djgreeb/Technics_SL-DZ1200_new_life/CNC/Spindel/shpinder.jpg

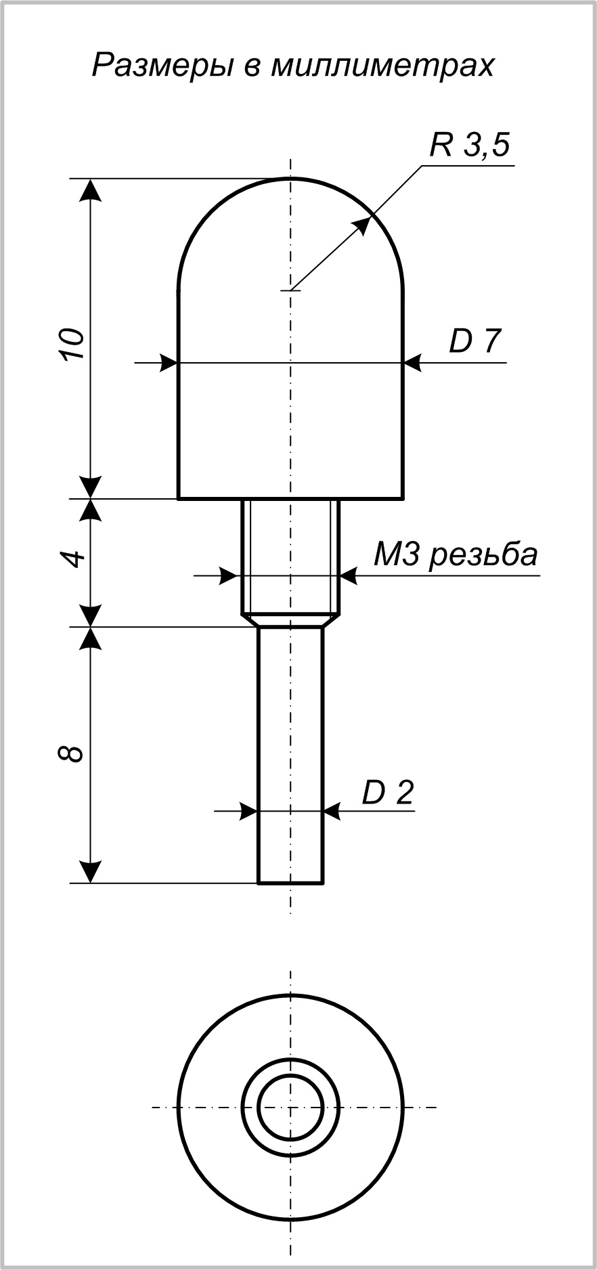
CNC/Spindel/shpinder.jpg
