djgreeb/Technics_SL-DZ1200_new_life/KiCad pcb project/SLDZ_Lay2.jpg

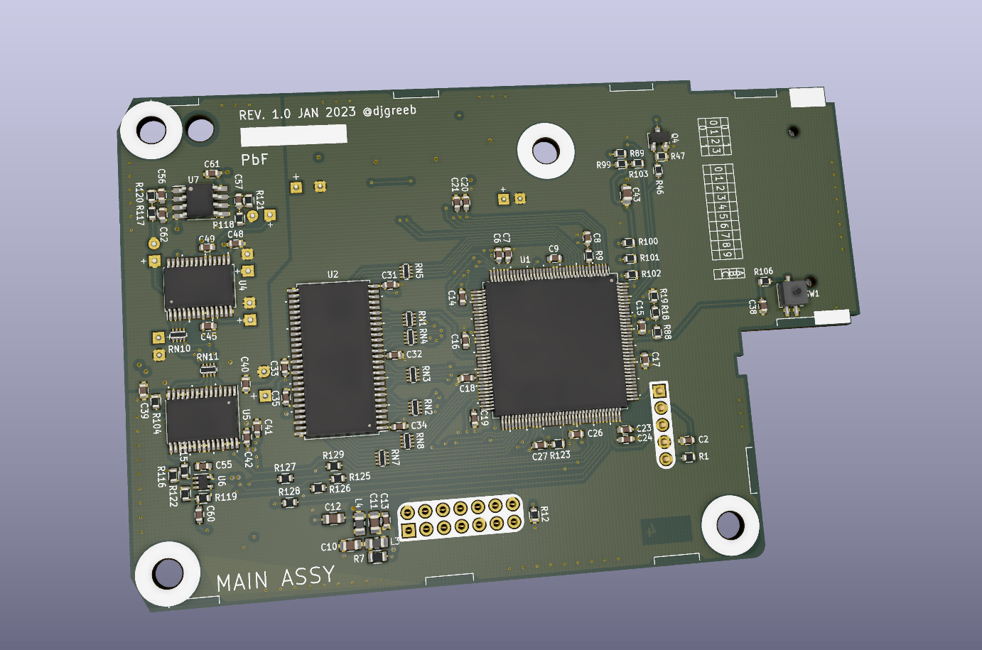
KiCad pcb project/SLDZ_Lay2.jpg
