djgreeb/Technics_SL-DZ1200_new_life/notes/Direct Drive signal control.JPG

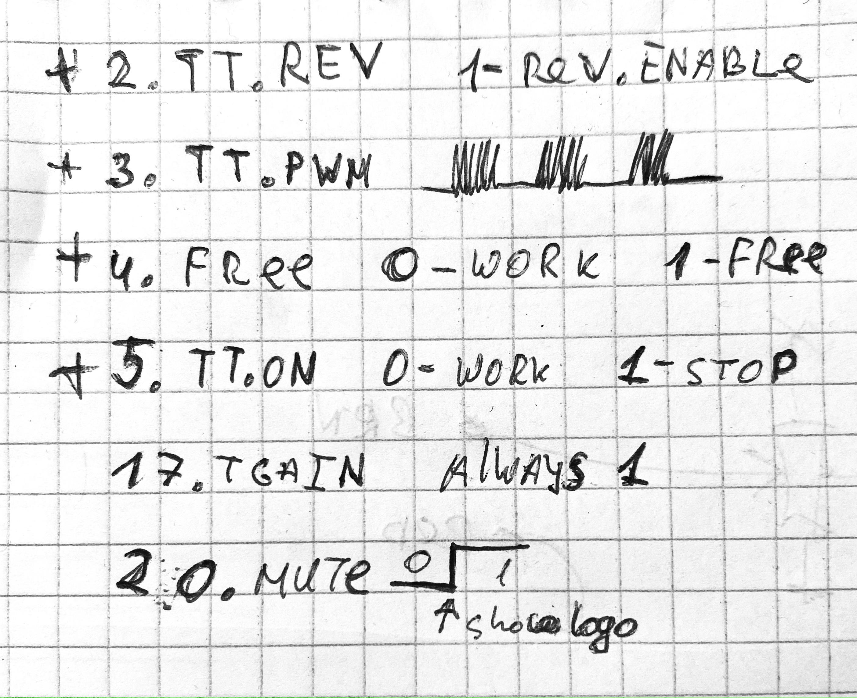
notes/Direct Drive signal control.JPG
