djgreeb/Technics_SL-DZ1200_new_life/Original DAC init data/DAC init.JPG

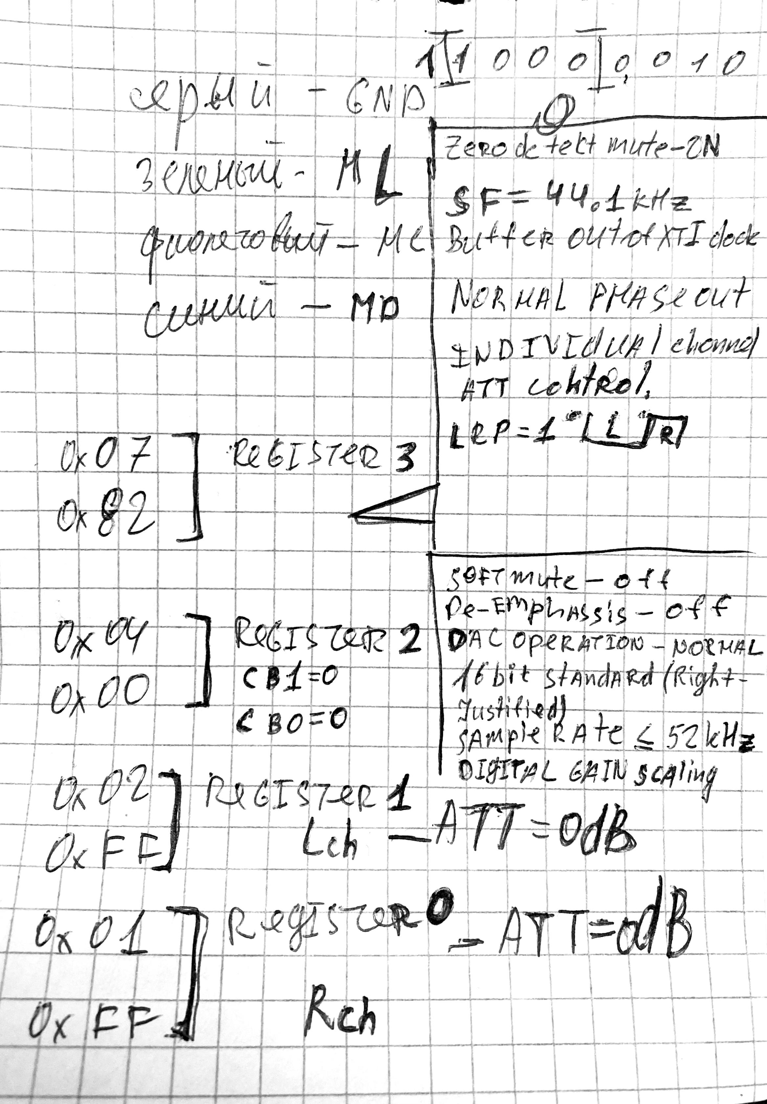
Original DAC init data/DAC init.JPG
