djgreeb/Technics_SL-DZ1200_new_life/Photo/IMG_2577.jpg

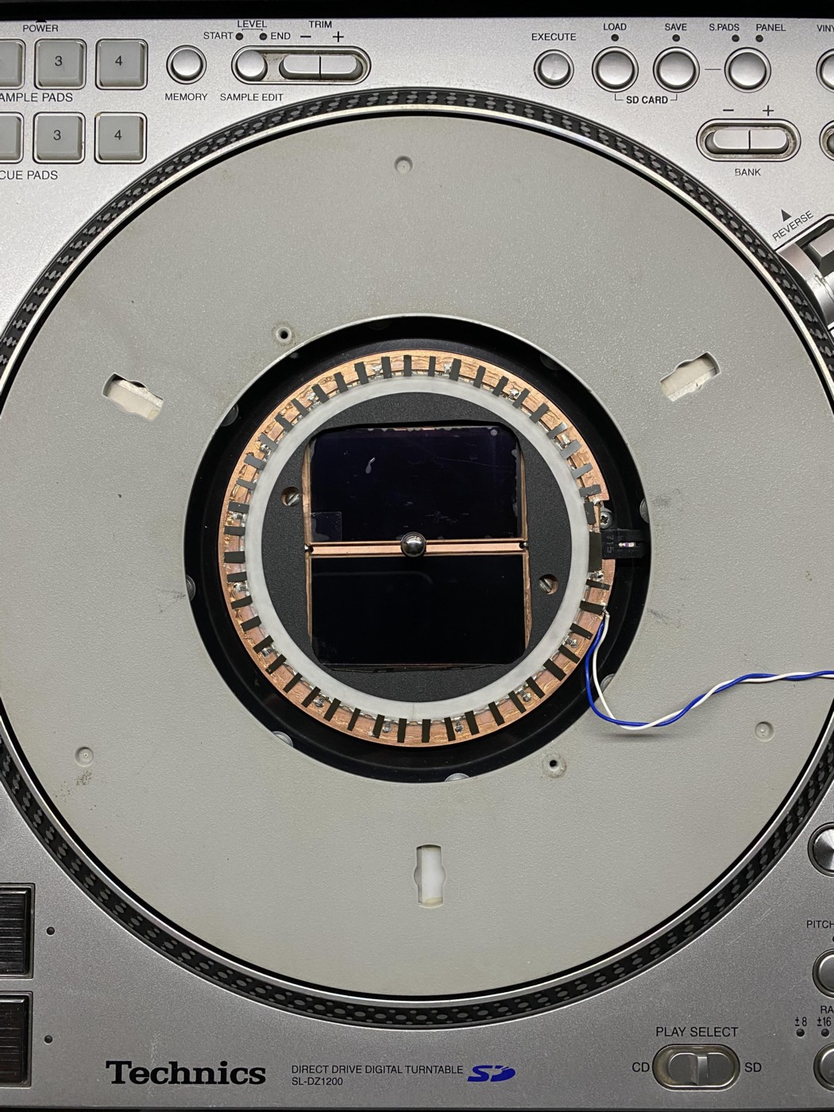
Photo/IMG_2577.jpg
