djgreeb/Technics_SL-DZ1200_new_life/Photo/IMG_2646.jpg

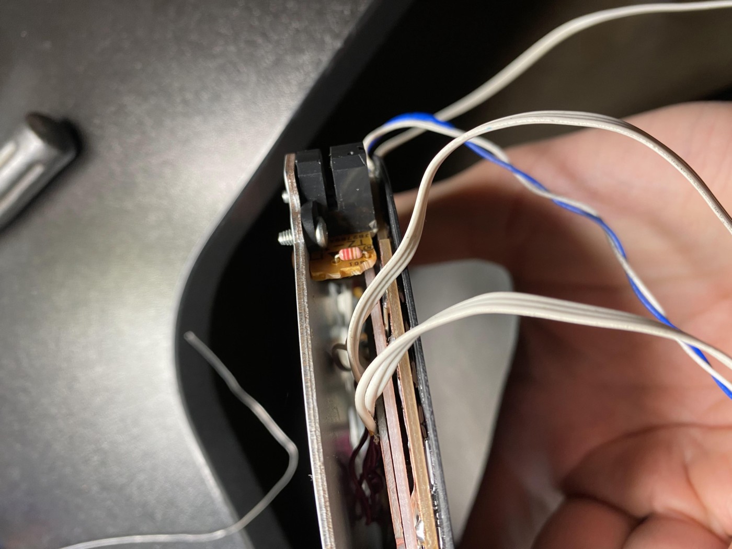
Photo/IMG_2646.jpg
