djgreeb/Technics_SL-DZ1200_new_life/Photo/IMG_2647.jpg

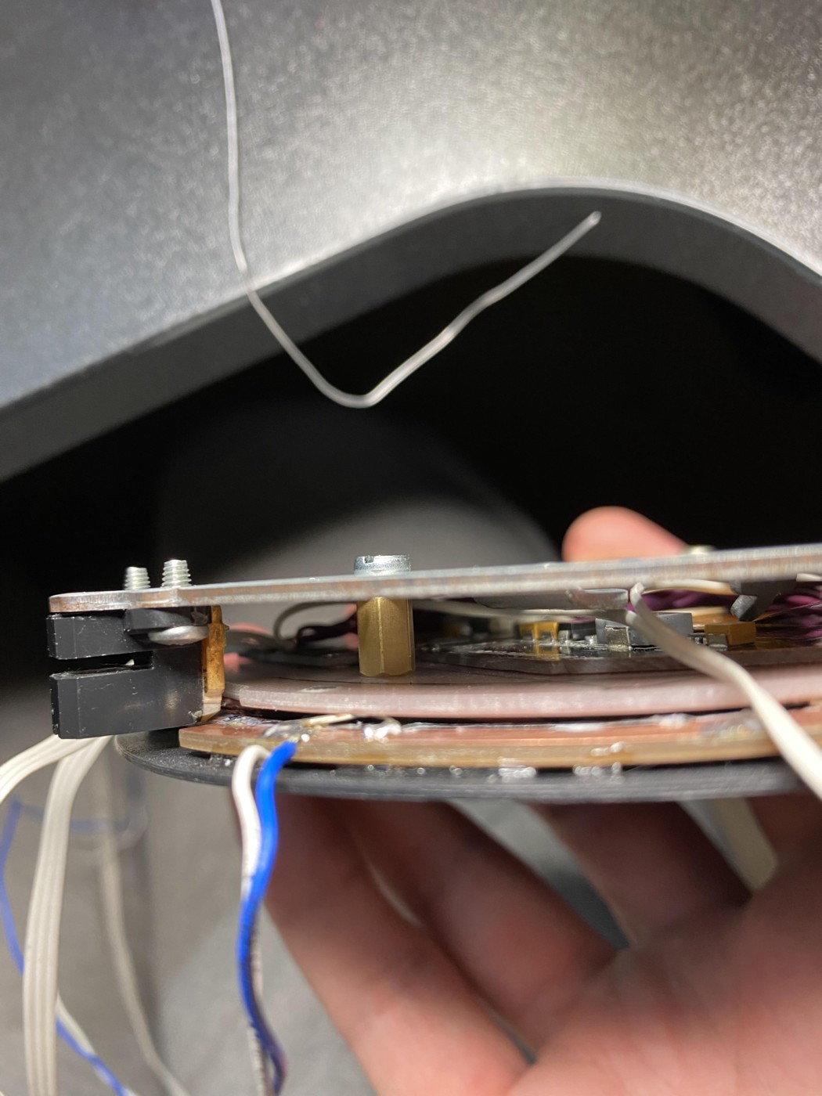
Photo/IMG_2647.jpg
