djgreeb/Technics_SL-DZ1200_new_life/Photo/IMG_3455.jpg

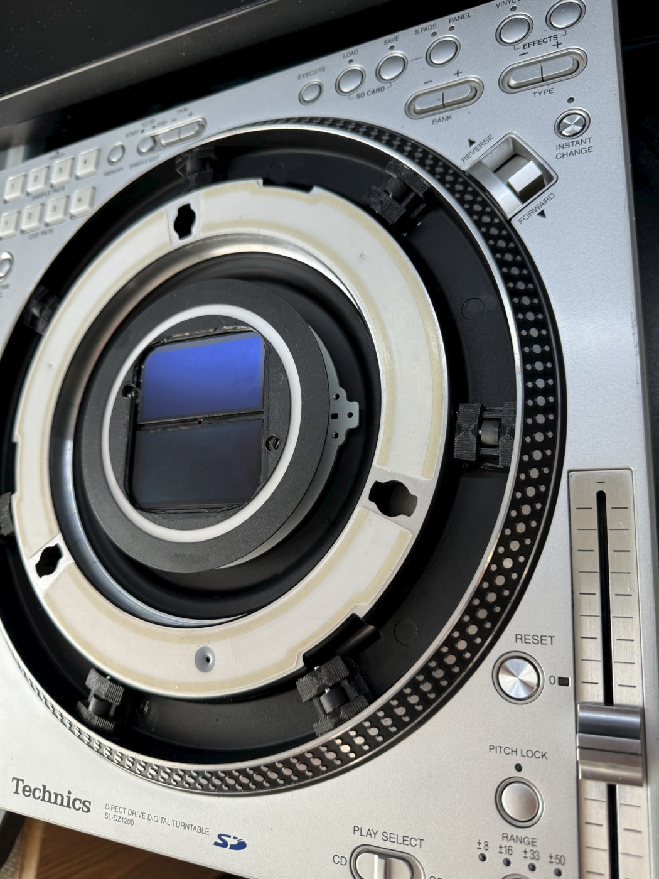
Photo/IMG_3455.jpg
