djgreeb/Technics_SL-DZ1200_new_life/Photo/IMG_8790.jpg

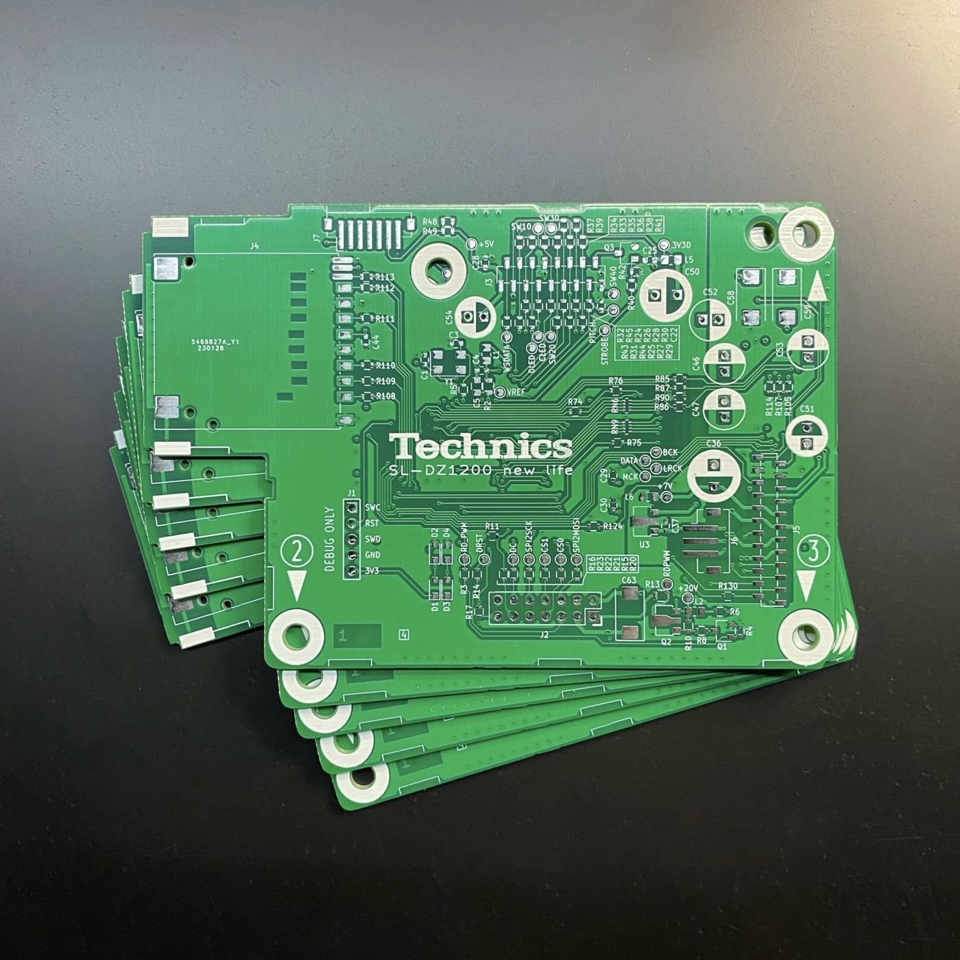
Photo/IMG_8790.jpg
