djgreeb/Technics_SL-DZ1200_new_life/Photo/IMG_8842.jpg

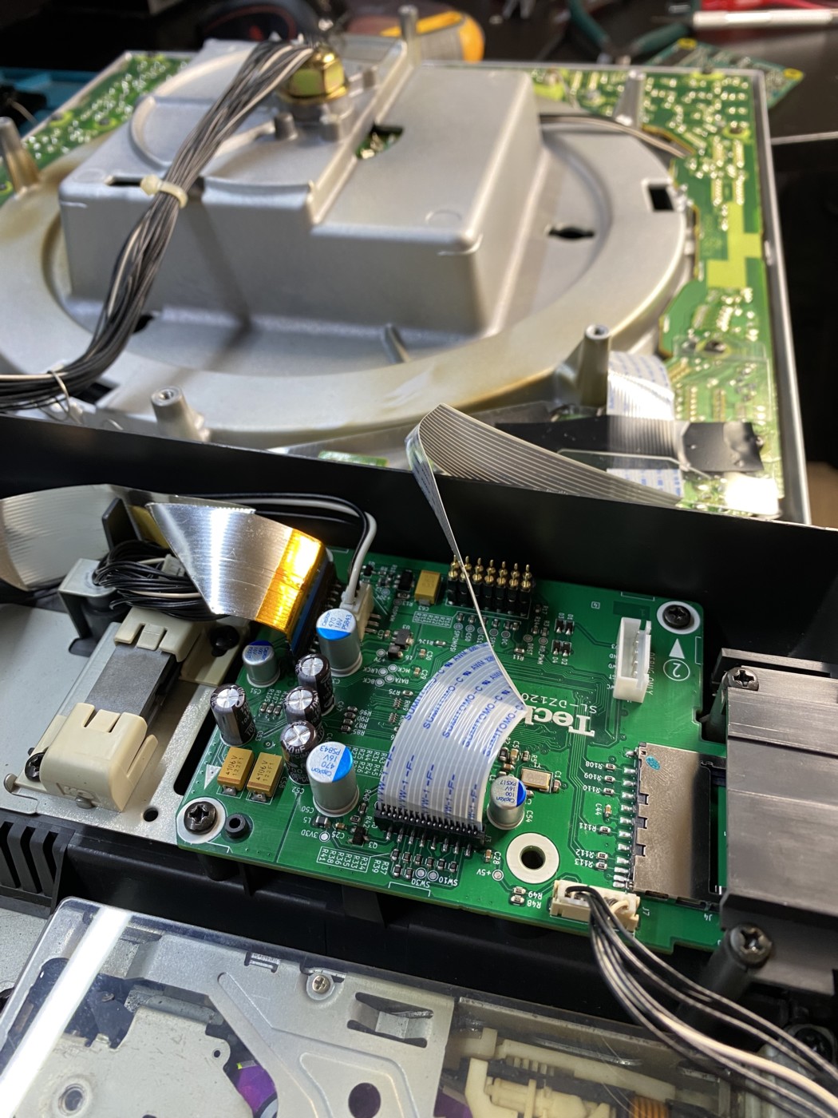
Photo/IMG_8842.jpg
