djgreeb/Technics_SL-DZ1200_new_life/Photo/IMG_8844.jpg

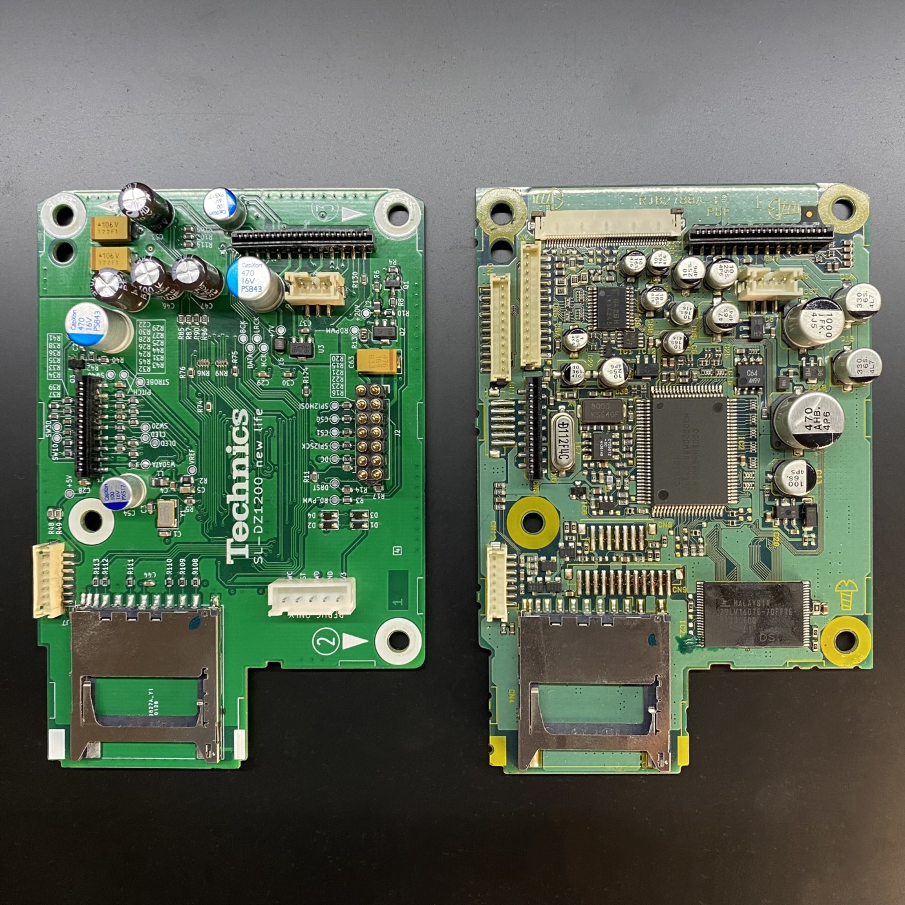
Photo/IMG_8844.jpg
