djgreeb/Technics_SL-DZ1200_new_life/Photo/IMG_8845.jpg

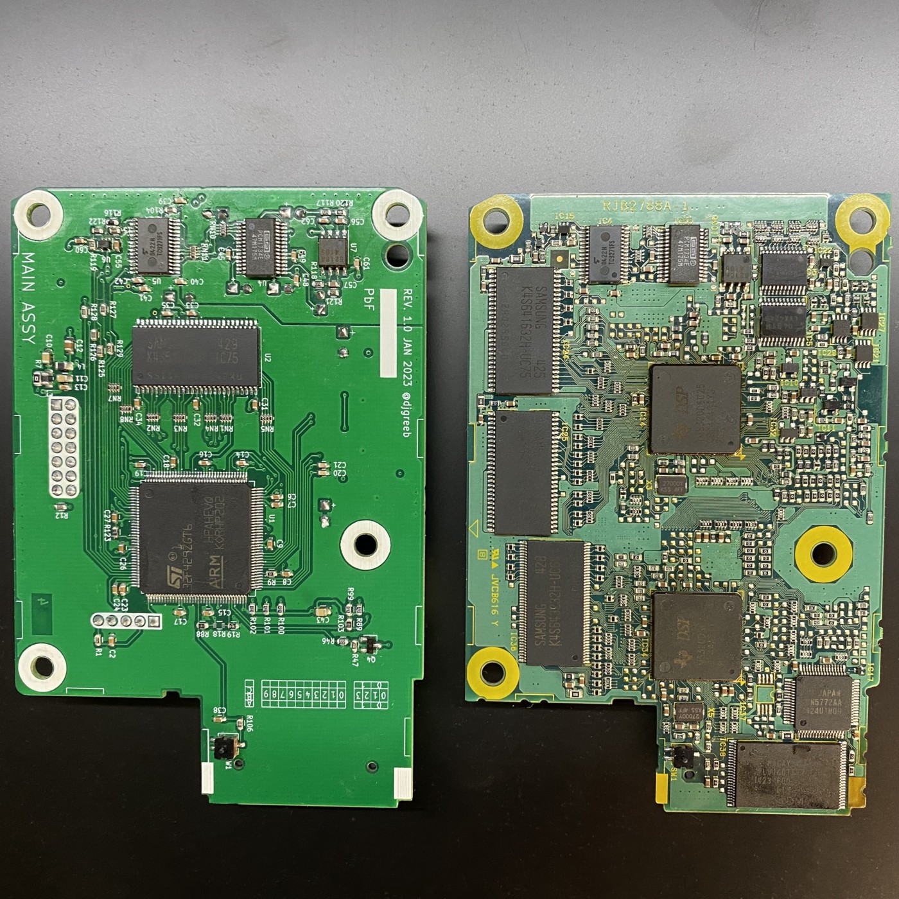
Photo/IMG_8845.jpg
