djgreeb/Technics_SL-DZ1200_new_life/Preparation of origin PCBs/IMG_4537.JPG

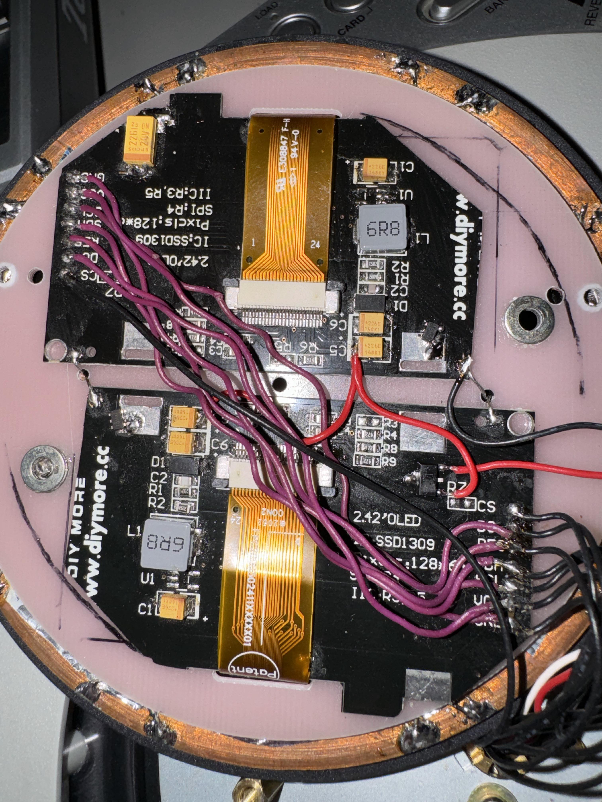
Preparation of origin PCBs/IMG_4537.JPG
