djgreeb/Technics_SL-DZ1200_new_life/Preparation of origin PCBs/IMG_9341.JPG

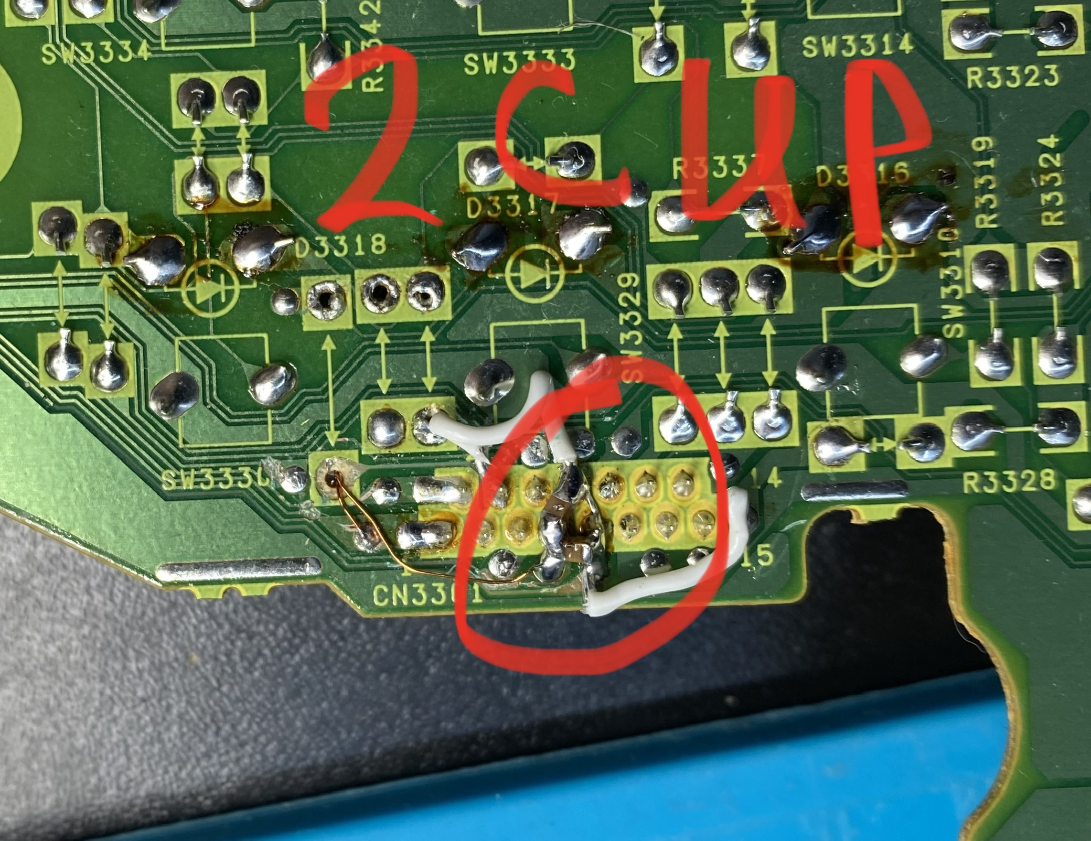
Preparation of origin PCBs/IMG_9341.JPG
