djgreeb/Technics_SL-DZ1200_new_life/Vinyl Encoder freq/DS2_20220222233140.png

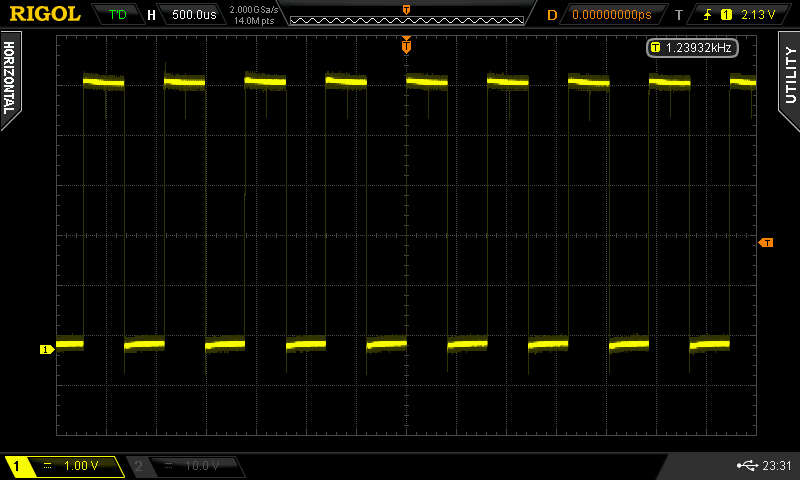
Vinyl Encoder freq/DS2_20220222233140.png
