djgreeb/Technics_SL-DZ1200_new_life/code/SLDZ/Inc/pads_color.h

/////////////////////////////////////////////////////////////////////////////////////////////////
// colors palettes for RGB leds and spi buffer for loading colors
//	product: Technics SL-DZ1200 new life
//
//
//
//
//	Author: Anatska Andrei
//
/////////////////////////////////////////////////////////////////////////////////////////////////
uint8_t PAD_BUF[100] =  {0x88, 0x88, 0x88, 0x88,
											0x88, 0x88, 0x88, 0x88,
											0x88, 0x88, 0x88, 0x88,
											0x88, 0x88, 0x88, 0x88,
											0x88, 0x88, 0x88, 0x88,
											0x88, 0x88, 0x88, 0x88,
											0x88, 0x88, 0x88, 0x88,
											0x88, 0x88, 0x88, 0x88,
											0x88, 0x88, 0x88, 0x88,
											0x88, 0x88, 0x88, 0x88,
											0x88, 0x88, 0x88, 0x88,
											0x88, 0x88, 0x88, 0x88,
											0x88, 0x88, 0x88, 0x88,
											0x88, 0x88, 0x88, 0x88,
											0x88, 0x88, 0x88, 0x88,
											0x88, 0x88, 0x88, 0x88,
											0x88, 0x88, 0x88, 0x88,
											0x88, 0x88, 0x88, 0x88,
											0x88, 0x88, 0x88, 0x88,
											0x88, 0x88, 0x88, 0x88,
											0x88, 0x88, 0x88, 0x88,
											0x88, 0x88, 0x88, 0x88,
											0x88, 0x88, 0x88, 0x88,
											0x88, 0x88, 0x88, 0x88, 
											0x00, 0x00, 0x00, 0x00};

const static uint32_t PADS_COLOR[6] = {0xFF2B0000,			//red
																			 0xFF002000,			//green
																			 0xFF190800,			//orange
																			 0xFF000035,			//blue
																			 0xFF302011,			//white
																			 0xFF010101				//black
																			 };	
										
#define ACTIVE_PAD_COLOR 0x00494949		
														
////////////////////////////////////////////////////////////////////////////////////////////////////////////////////////
