djgreeb/Technics_SL-DZ1200_new_life/Preparation of origin PCBs/IMG_8903.JPG

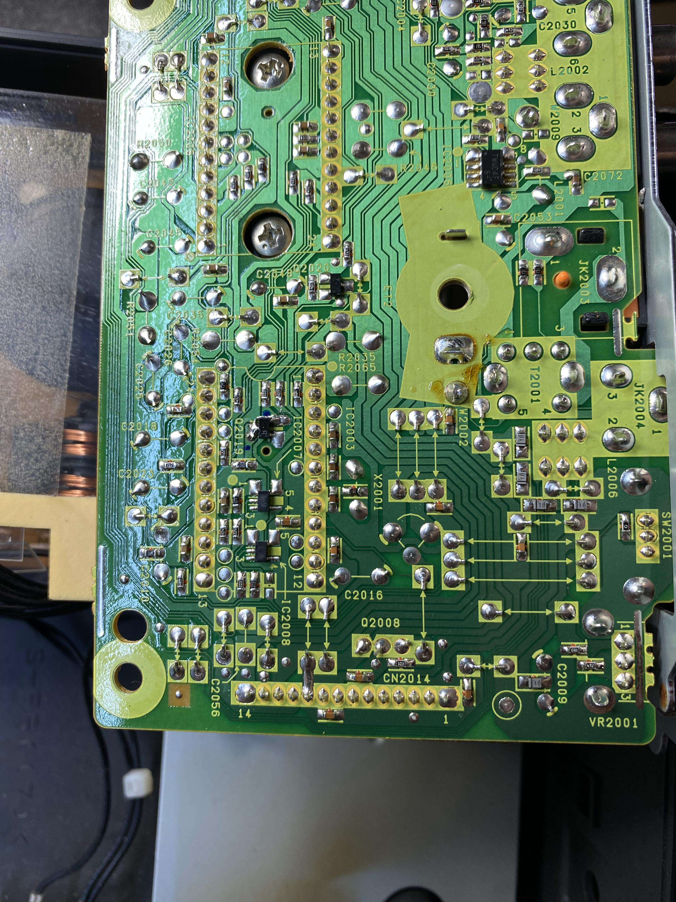
Preparation of origin PCBs/IMG_8903.JPG
